dexhoui/Edge-Computing-Sensor-Kit/assets/images/ECSK.jpg

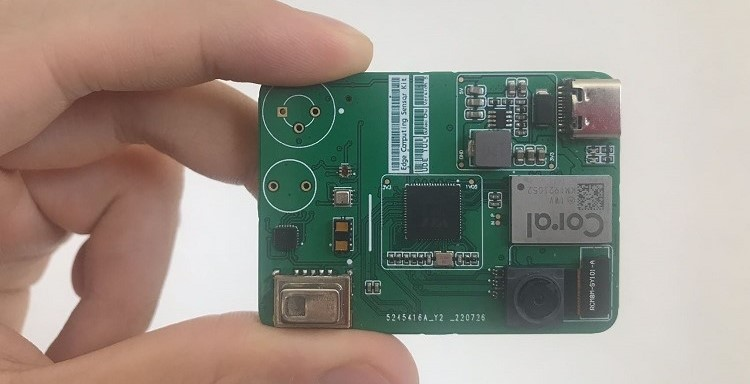
assets/images/ECSK.jpg
