dexhoui/Edge-Computing-Sensor-Kit/software/application/assets/img/application.png

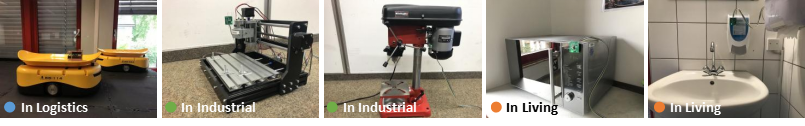
software/application/assets/img/application.png
