dexhoui/Edge-Computing-Sensor-Kit/software/application/assets/img/ecsk1.jpg

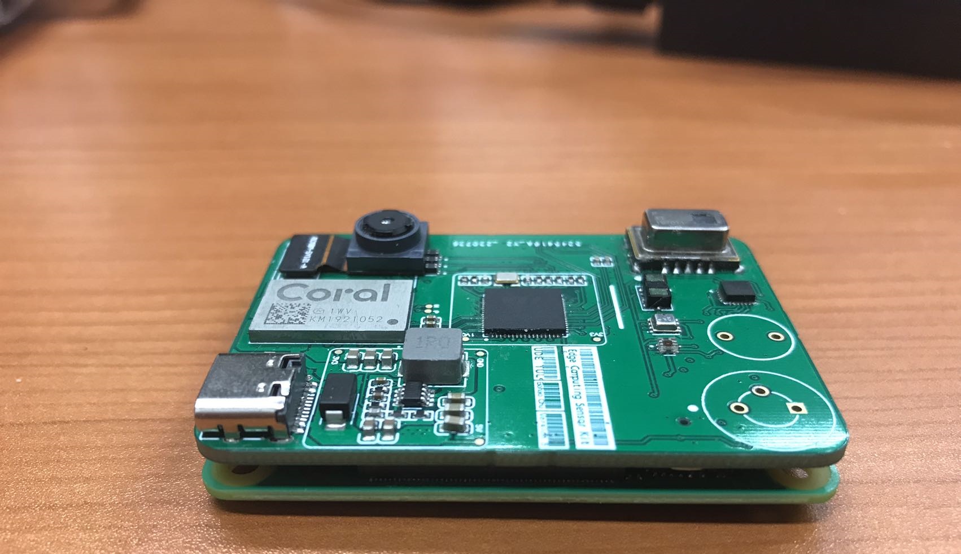
software/application/assets/img/ecsk1.jpg
