dexhoui/Edge-Computing-Sensor-Kit/software/application/assets/img/img.png

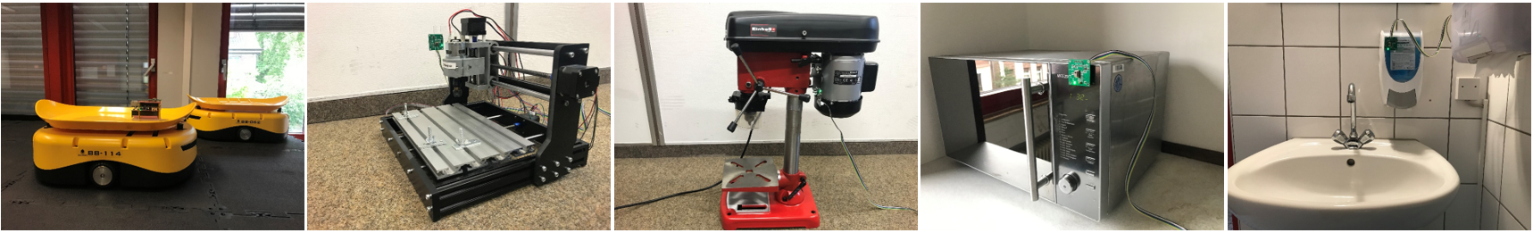
software/application/assets/img/img.png
