dexhoui/Edge-Computing-Sensor-Kit/software/application/assets/img/wc.jpg

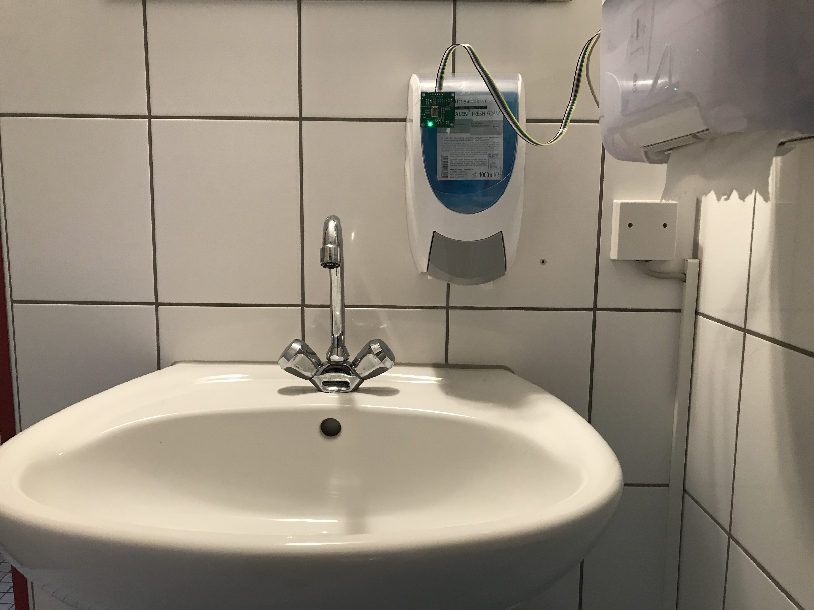
software/application/assets/img/wc.jpg
