dexhoui/Edge-Computing-Sensor-Kit/software/edge/assets/images/edge/eye1.png

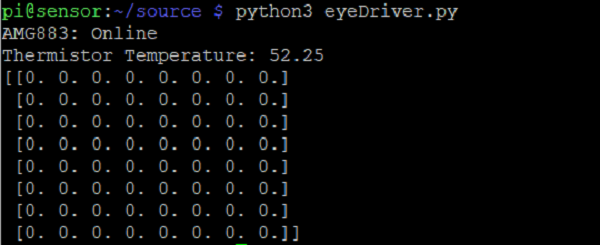
software/edge/assets/images/edge/eye1.png
