dexhoui/Edge-Computing-Sensor-Kit/software/edge/assets/images/edge/pycham8.png

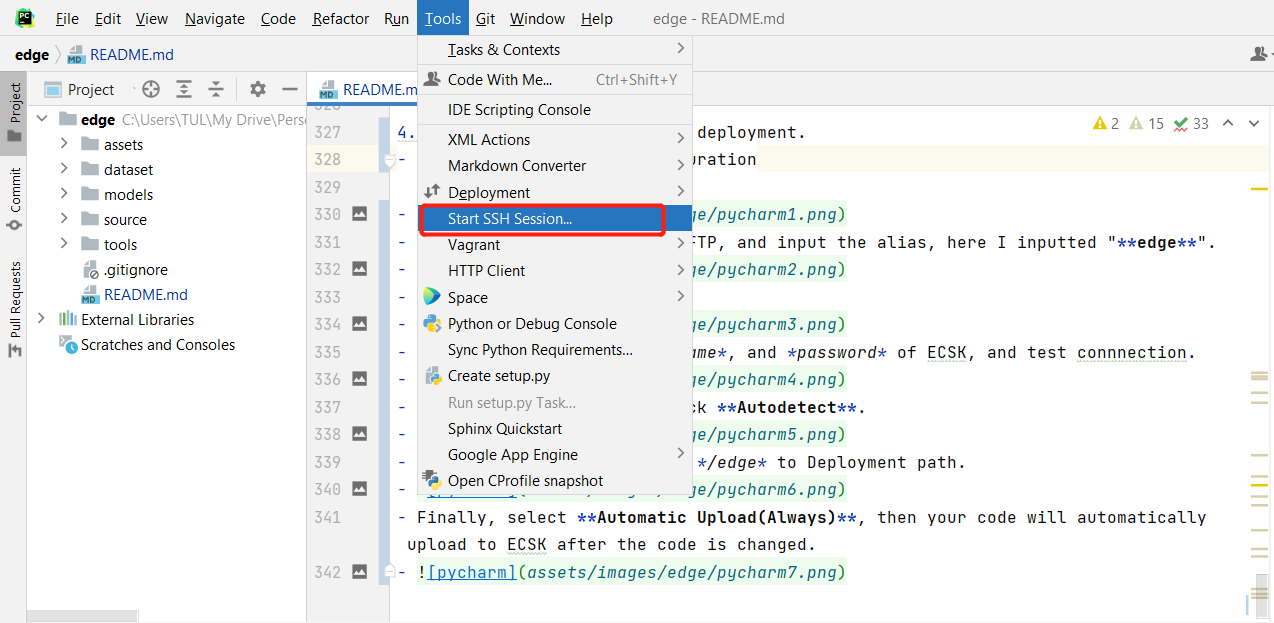
software/edge/assets/images/edge/pycham8.png
